LemonAidLee/Precision-Analog-Front-End/docs/images/ltspice/ltspice_filter_gain_chain_transient_500hz.png

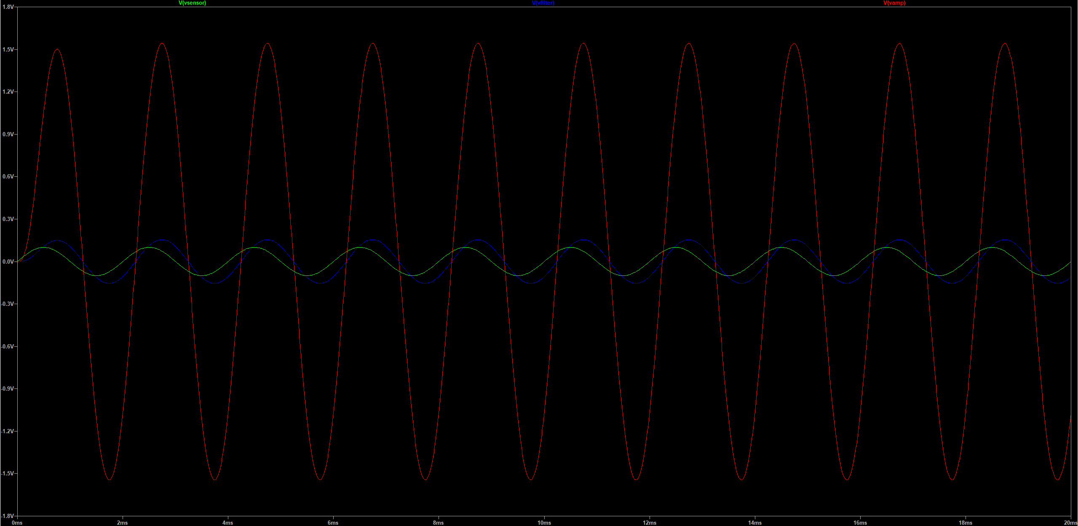
docs/images/ltspice/ltspice_filter_gain_chain_transient_500hz.png
