LemonAidLee/Precision-Analog-Front-End/Precision DAQ AFE_Documentation/LTSpice Simulation Image/AFE_CompleteIntegratedCircuit.png

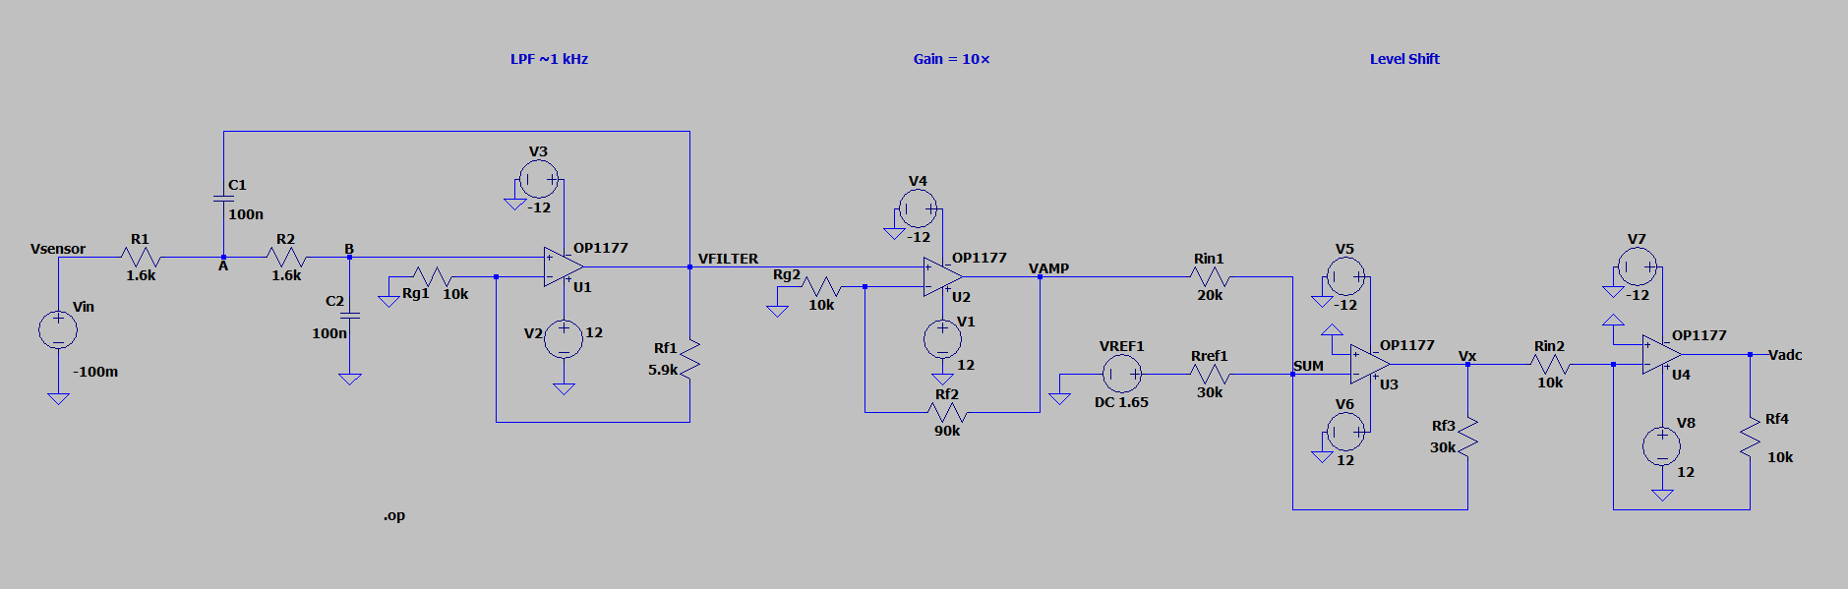
Precision DAQ AFE_Documentation/LTSpice Simulation Image/AFE_CompleteIntegratedCircuit.png
