LemonAidLee/Precision-Analog-Front-End/Precision DAQ AFE_Documentation/LTSpice Simulation Image/AFE_LevelShifter_Circuit.png

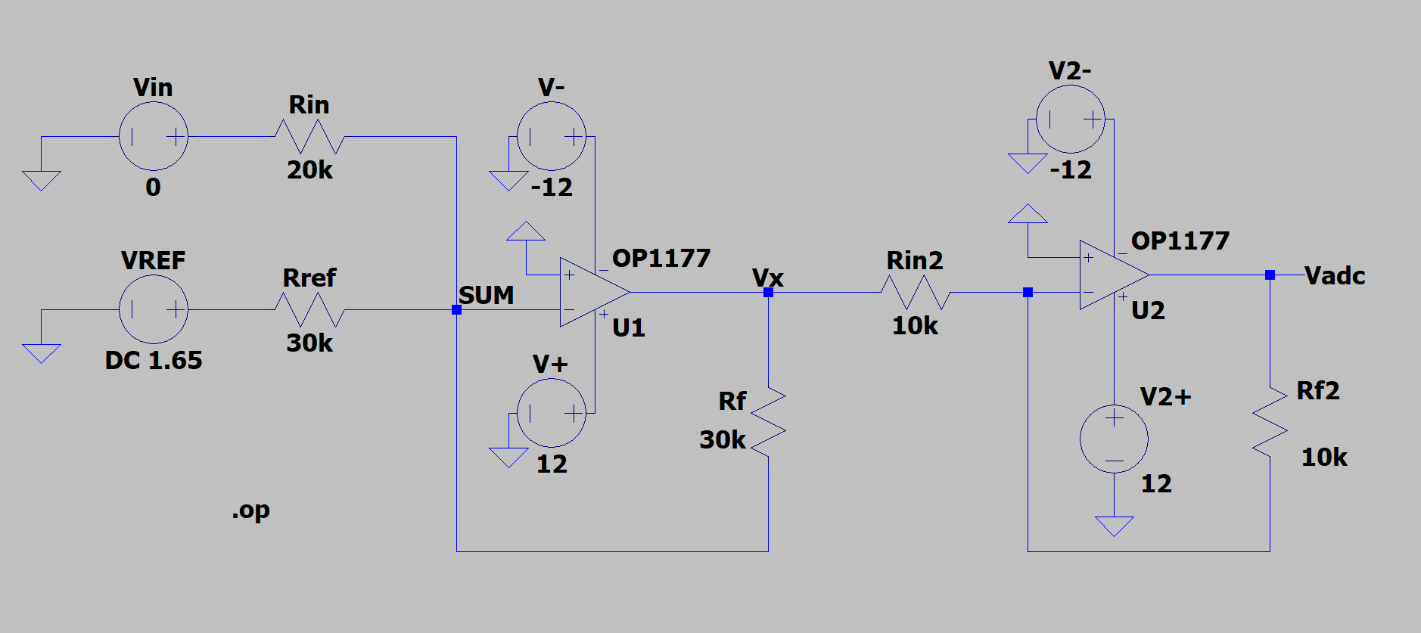
Precision DAQ AFE_Documentation/LTSpice Simulation Image/AFE_LevelShifter_Circuit.png
