LemonAidLee/Precision-Analog-Front-End/Precision DAQ AFE_Documentation/LTSpice Simulation Image/AFE_SallenKey_OP1177_BodePlotAnalysis.png

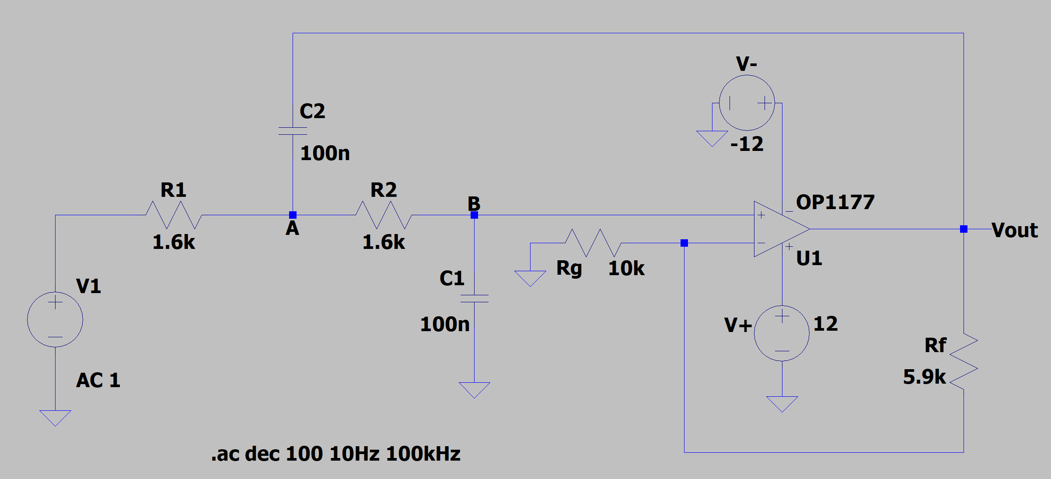
Precision DAQ AFE_Documentation/LTSpice Simulation Image/AFE_SallenKey_OP1177_BodePlotAnalysis.png
