LemonAidLee/Precision-Analog-Front-End/Precision DAQ AFE_Documentation/LTSpice Simulation Image/TransferEquation_Waveform.png

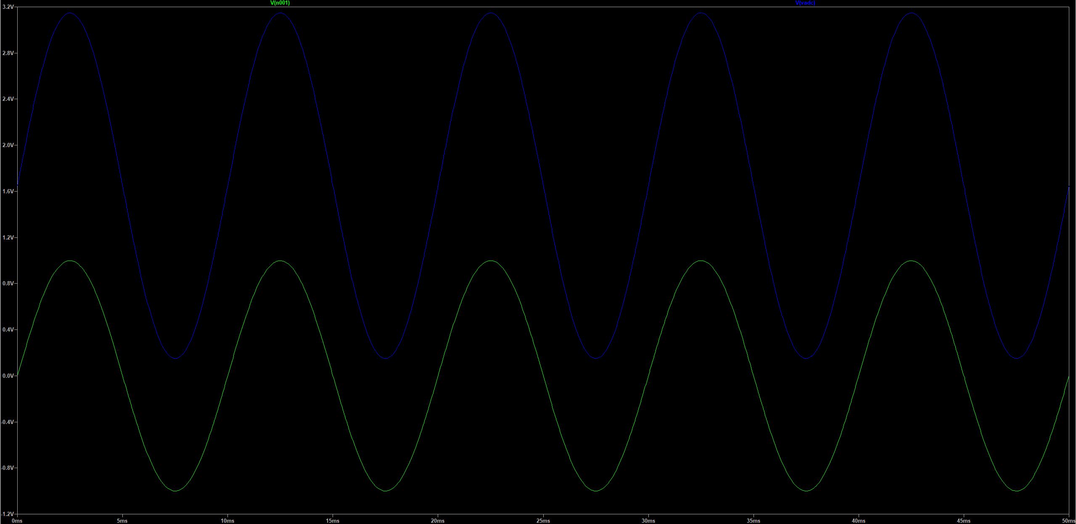
Precision DAQ AFE_Documentation/LTSpice Simulation Image/TransferEquation_Waveform.png
