LemonAidLee/Precision-Analog-Front-End/LTSpice_Simulation/AFE_SallenKey_R1p5k_DCstep_test.asc

C1: cap; 100n
C2: cap; 100n
R1: res; 1.5k
R2: res; 1.5k
Rf: res; 5.9k
Rg: res; 10k
U1: OP1177
V1: voltage; PWL(0 0 1m 0 1.001m 0.1 2m 0.1 2.001m -0.1 3m -0.1)
V+: voltage; 12
V-: voltage; -12
Named nets: A, B, 0, Vout
.tran 0 3.5m 0 10u
.meas TRAN V_zero FIND V(vout) AT 0.5m
.meas TRAN V_pos100m FIND V(vout) AT 1.5m
.meas TRAN V_neg100m FIND V(vout) AT 2.5m
