LemonAidLee/Precision-Analog-Front-End/LTSpice_Simulation/AFE_SallenKey_R1p5k_test.asc

C1: cap; 100n
C2: cap; 100n
R1: res; 1.5k
R2: res; 1.5k
Rf: res; 5.9k
Rg: res; 10k
U1: OP1177
V1: voltage; ""; AC 1
V+: voltage; 12
V-: voltage; -12
Named nets: A, B, 0, Vout
.ac dec 100 10Hz 100kHz
.meas AC Vout_max MAX mag(V(vout))
.meas AC f_3db WHEN mag(V(vout))=Vout_max/sqrt(2) CROSS=1
.meas AC Gain_pass_dB FIND Vdb(vout) AT 10
.meas AC Gain_pass_lin FIND mag(V(vout)) AT 10
