LemonAidLee/Precision-Analog-Front-End/LTSpice_Simulation/AFE_Amplifier.asc

Rf: res; 90k
Rg: res; 10k
U1: OP1177
V+: voltage; 12
V-: voltage; -12
Vin: voltage; ""; SINE(0 0.1 10000)
Named nets: 0, Vout
.tran 0 2m 0 100n
