LemonAidLee/Precision-Analog-Front-End/LTSpice_Simulation/AFE_Filter_01_RC.asc

C1: cap; 100n
R1: res; 1.6k
V1: voltage; ""; AC 1
Named nets: Vout, 0
.ac dec 100 10 100k
