LemonAidLee/Precision-Analog-Front-End/LTSpice_Simulation/AFE_Integration.asc

C1: cap; 100n
C2: cap; 100n
R1: res; 1.6k
R2: res; 1.6k
Rf1: res; 5.9k
Rf2: res; 90k
Rg1: res; 10k
Rg2: res; 10k
U1: OP1177
U2: OP1177
V1: voltage; 12
V2: voltage; 12
V3: voltage; -12
V4: voltage; -12
Vin: voltage; ""; SINE(0 0.1 1000)
Named nets: A, B, 0, VFILTER, VAMP, Vsensor
.tran 0 10m 0 1u
