LemonAidLee/Precision-Analog-Front-End/LTSpice_Simulation/AFE_Integration_TL082.asc

C1: cap; 100n
C2: cap; 100n
Cvref: cap; 100n
R1: res; 1.5k
R2: res; 1.5k
Rf1: res; 5.9k
Rf2: res; 90k
Rf3: res; 30k
Rf4: res; 10k
Rg1: res; 10k
Rg2: res; 10k
Rin1: res; 36k
Rin2: res; 10k
Rref1: res; 30k
Rref_a1: res; 470
Rref_b1: res; 470
U1: opamp2; TL082
U2: opamp2; TL082
U3: opamp2; TL082
U4: opamp2; TL082
V3V3: voltage; 3.3
V12N: voltage; -12
V12P: voltage; 12
Vsensor: voltage; 0
Named nets: VSENSOR, A, B, N1A, VFILTER, N1B, VAMP, +3V3, VREF, SUM, VX, N2B, VADC, +12V, -12V, 0
AFE Integration - TL082 verification build. Same topology/values as AFE_IntegrationComplete.asc (OP1177). Compare VADC vs OP1177 reference.
VREF divider: 3.3V x 470/(470+470) = 1.65V, 100nF bypass
Stage 1: Input/LPF (U1, TL082) -> VFILTER = 1.59 x Vsensor
Stage 2: Gain (U2, TL082) -> VAMP = 10 x VFILTER
Stage 3: Level shift (U3, TL082) -> VX = -(30k/36k)*VAMP - VREF
Stage 4: Final inverter (U4, TL082) -> VADC = -VX = 0.8333*VAMP + 1.65V
.dc Vsensor list 0 0.1 -0.1
.lib "D:\Progmata\Precision Mixed-Signal Data Acquisition Front End (AFE)\LTSpice_Simulation\TL082.lib"
