LemonAidLee/Precision-Analog-Front-End/LTSpice_Simulation/AFE_LevelShifter.asc

Rf2: res; 10k
Rf: res; 30k
Rin2: res; 10k
Rin: res; 36k
Rref: res; 30k
U1: OP1177
U2: OP1177
V2+: voltage; 12
V2-: voltage; -12
V+: voltage; 12
V-: voltage; -12
Vin: voltage; SINE(0 1 10000)
VREF: voltage; DC 1.65
Named nets: SUM, 0, Vx, Vadc
.op
.tran 0 2m 0 100n
