LemonAidLee/Precision-Analog-Front-End/LTSpice_Simulation/AFE_SallenKey_E_Source.asc

C1: cap; 100n
C2: cap; 100n
E1: e; 1e9
R1: res; 1.6k
R2: res; 1.6k
Rf: res; 5.9k
Rg: res; 10k
V1: voltage; ""; AC 1
Named nets: A, B, 0, Vout
.ac dec 100 10Hz 100kHz
