LemonAidLee/Precision-Analog-Front-End/LTSpice_Simulation/AFE_SallenKey_OP1177_Transient.asc

C1: cap; 100n
C2: cap; 100n
R1: res; 1.6k
R2: res; 1.6k
Rf: res; 5.9k
Rg: res; 10k
U1: OP1177
V+: voltage; 12
V-: voltage; -12
Vin: voltage; ""; SINE(0 1 10000)
Named nets: A, B, 0, Vout
.tran 0 2m 0 100n
